wryan67/5x7laser/photos/8A266A81-EDB7-455D-8486-B8DF81140D3A-2090-000001E31C5A7B8D.jpg

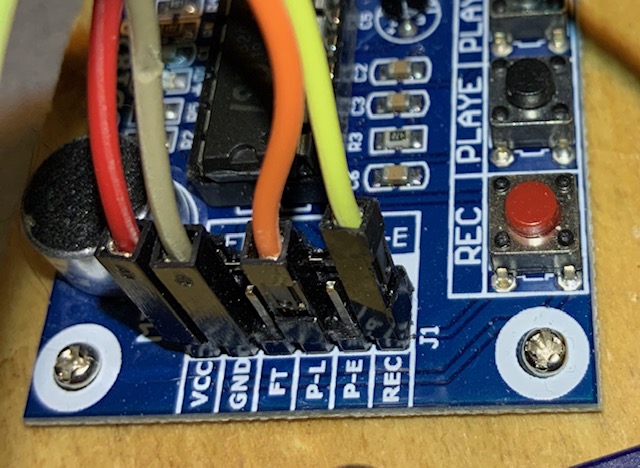
photos/8A266A81-EDB7-455D-8486-B8DF81140D3A-2090-000001E31C5A7B8D.jpg
