wryan67/5x7laser/photos/98A164D9-7E31-4DEC-9D0F-0AE598D2B0AE-2090-000001E5097991B9.jpg

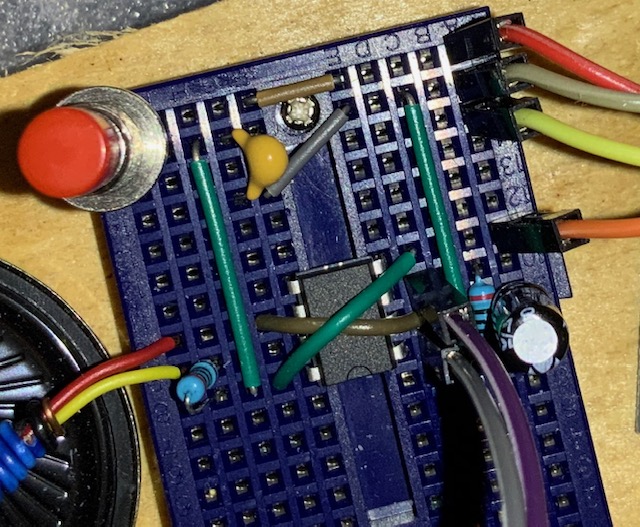
photos/98A164D9-7E31-4DEC-9D0F-0AE598D2B0AE-2090-000001E5097991B9.jpg
