wryan67/5x7laser/photos/C36D4584-9315-4CFA-A101-77AC29264F38-2090-000001E413C061C7.jpg

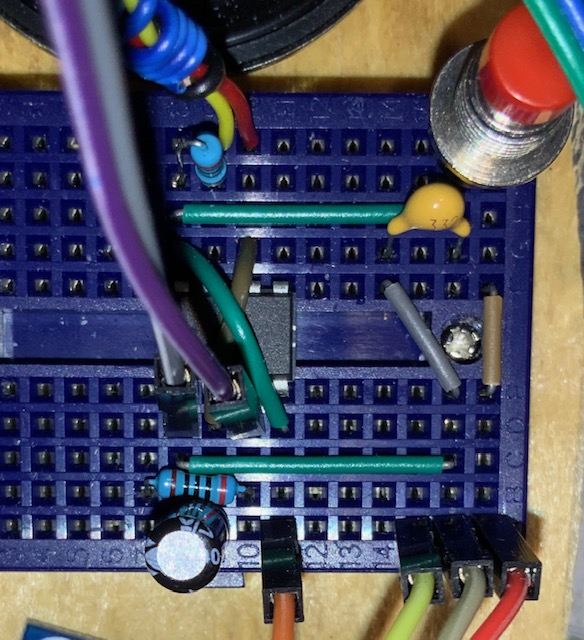
photos/C36D4584-9315-4CFA-A101-77AC29264F38-2090-000001E413C061C7.jpg
