wryan67/5x7laser/case/cnc/20mm spacer.dxf

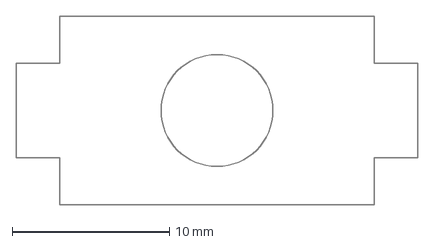
[picture p24: CAD file, 2023-05-02]
case/cnc/20mm spacer.dxf
25.5 x 12.0 mm
