wryan67/5x7laser/case/laser/save/plot-handle.dxf

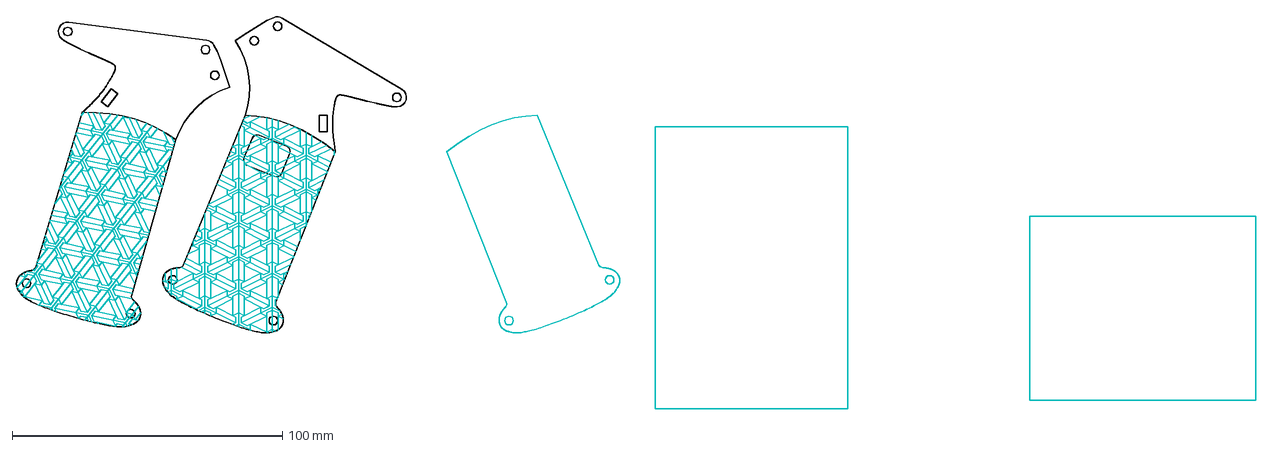
[picture p26: CAD file, 2023-05-02]
case/laser/save/plot-handle.dxf
458.9 x 145.3 mm
