wryan67/5x7laser/case/cnc/spacers.dxf

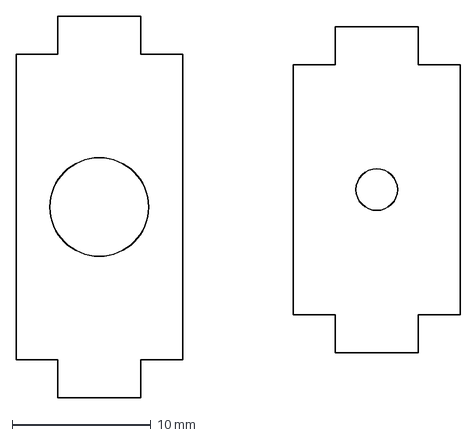
[picture p27: CAD file, 2023-05-02]
case/cnc/spacers.dxf
32.0 x 27.5 mm
