wryan67/5x7laser/case/laser/save/plot-case2m.dxf

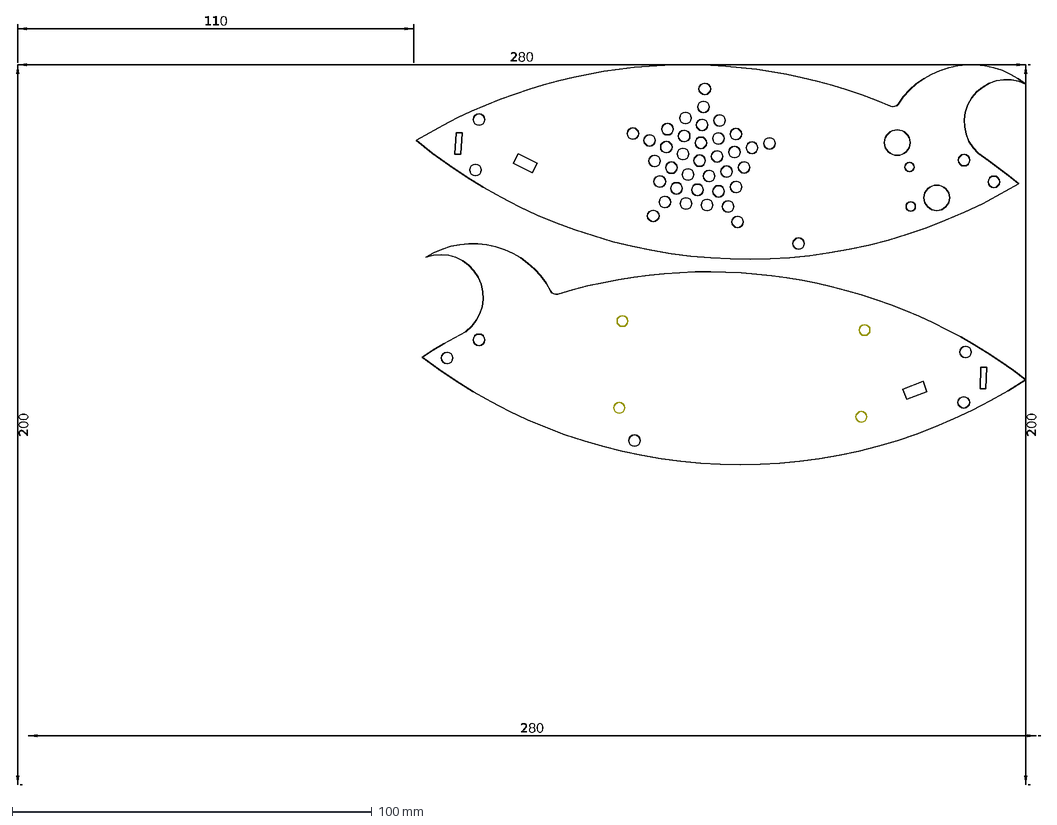
[picture p28: CAD file, 2023-05-02]
case/laser/save/plot-case2m.dxf
200
280
110
