wryan67/5x7laser/case/cnc/plot-handle-back.dxf

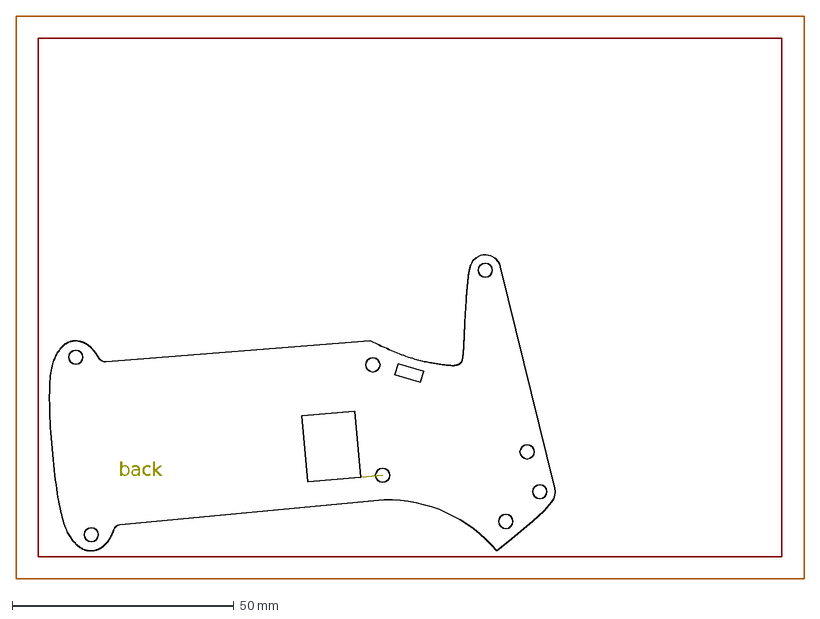
[picture p29: CAD file, 2023-05-02]
case/cnc/plot-handle-back.dxf
back
