wryan67/5x7laser/case/laser/plot-case2m.dxf

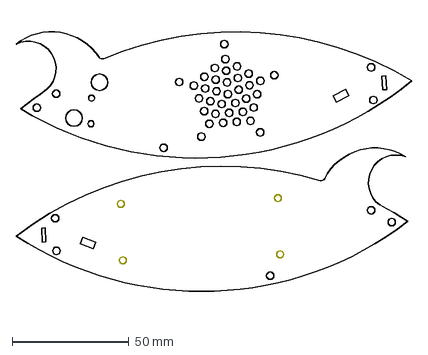
[picture p30: CAD file, 2023-05-02]
case/laser/plot-case2m.dxf
169.3 x 127.8 mm
