wryan67/5x7laser/case/laser/save/plot-case1f.dxf

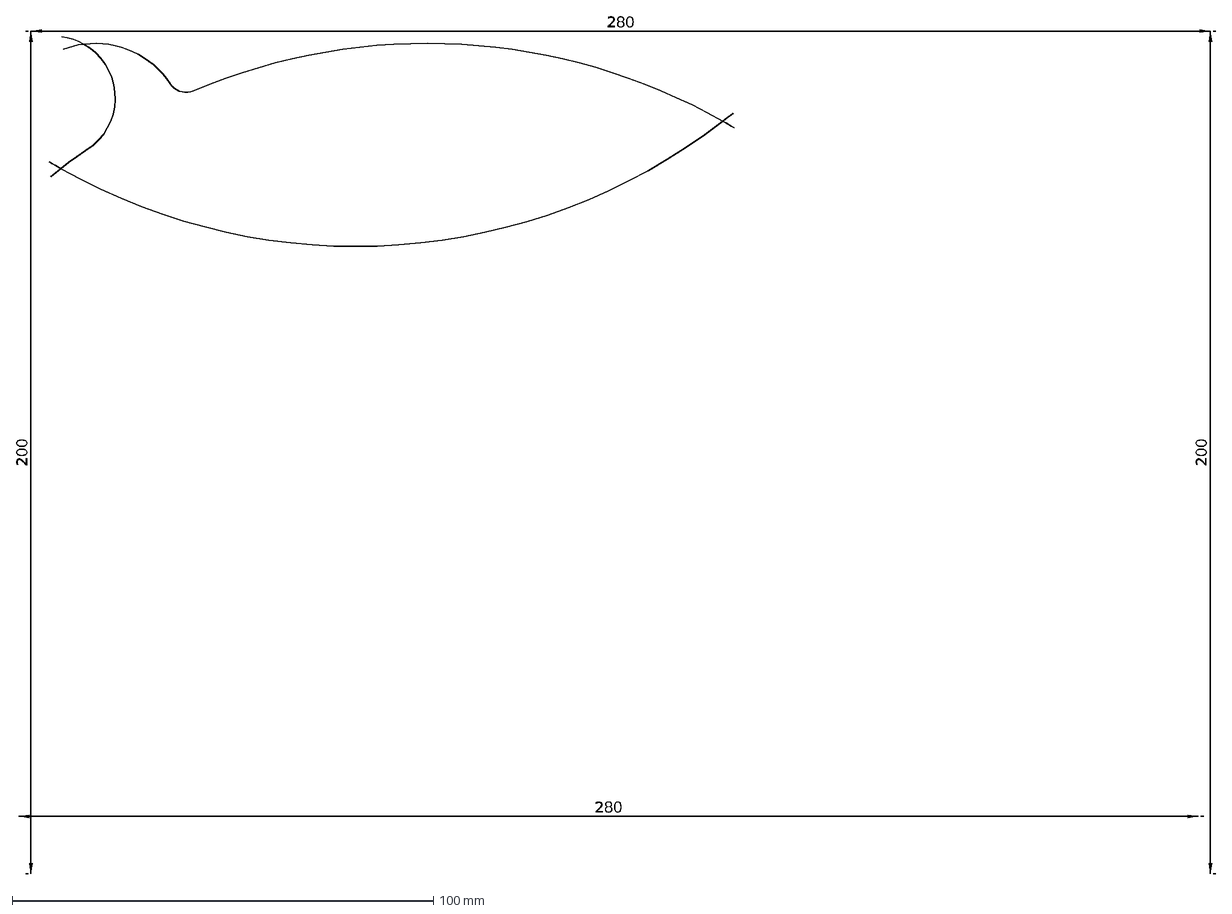
[picture p31: CAD file, 2023-05-02]
case/laser/save/plot-case1f.dxf
200
280
