wryan67/5x7laser/case/cnc/lasergun8.dxf

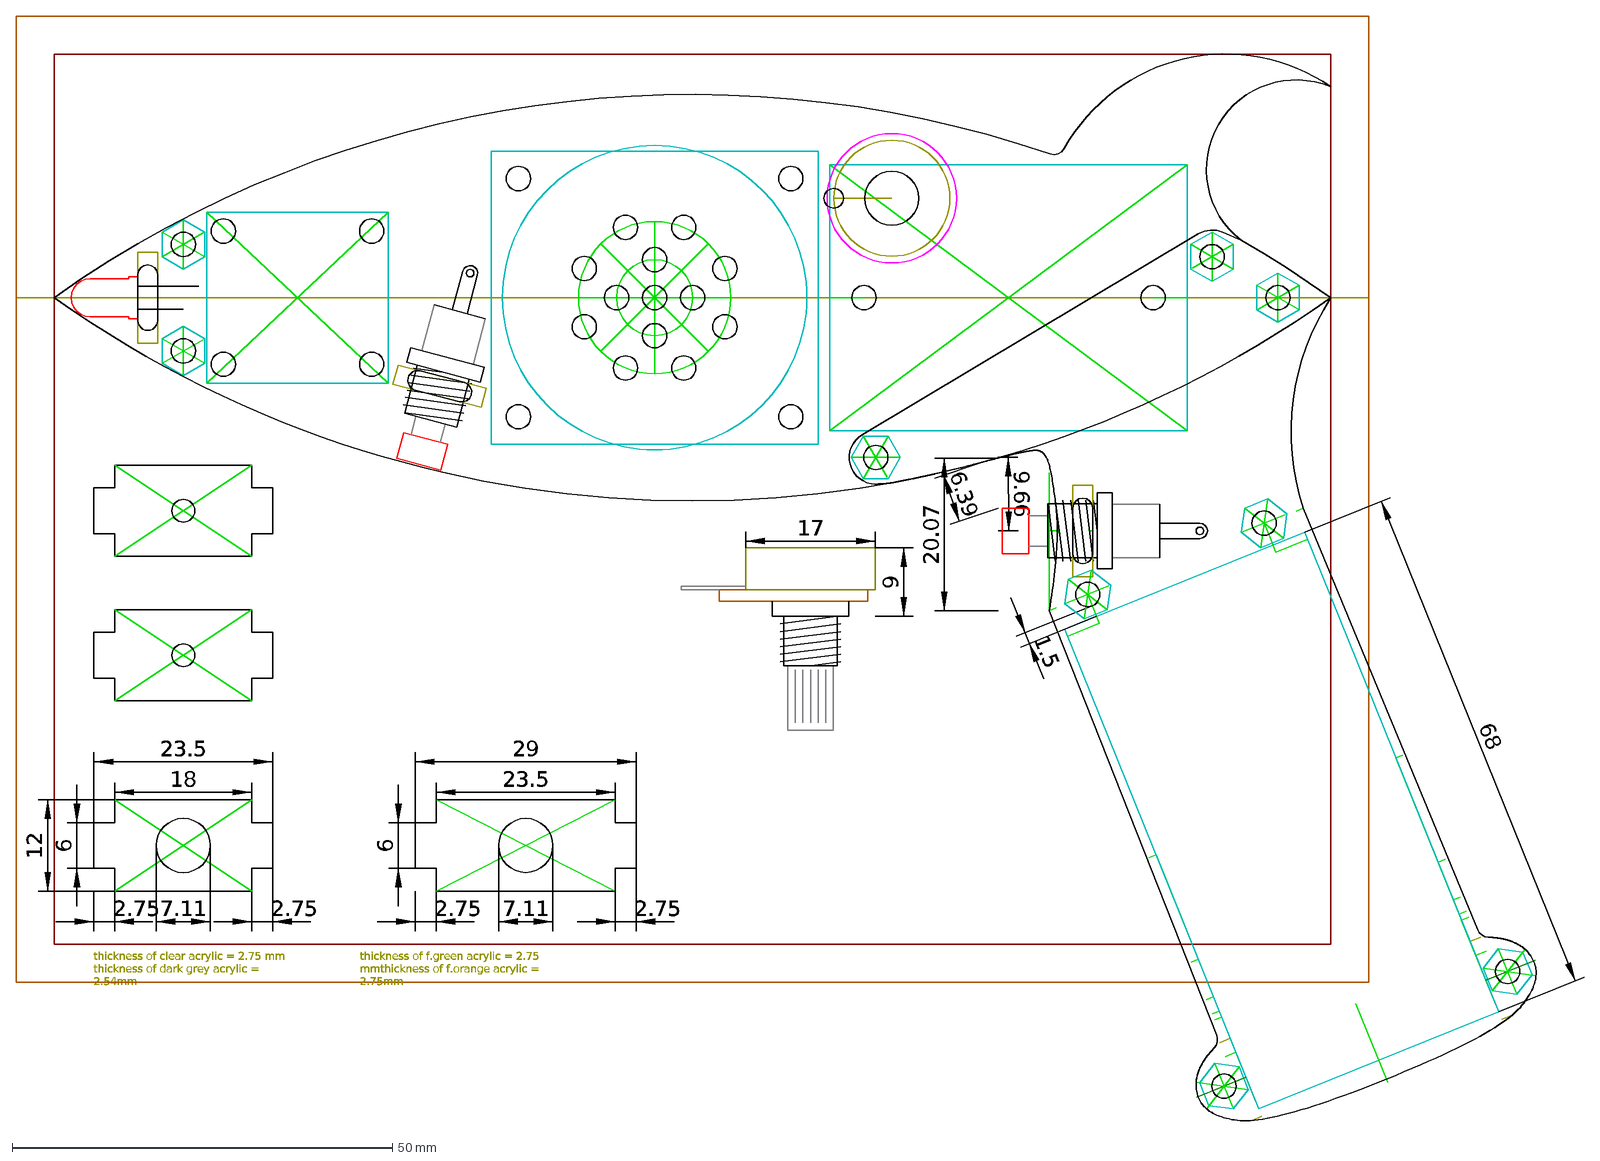
[picture p32: CAD file, 2023-05-02]
case/cnc/lasergun8.dxf
9
17
thickness of clear acrylic = 2.75 mm thickness of dark grey acrylic = 2.54mm
6
2.75
6.39
20.07
9.66
18
23.5
7.11
29
thickness of f.green acrylic = 2.75 mm thickness of f.orange acrylic = 2.75mm
1.5
68
12
