wryan67/5x7laser/case/laser/save/plot-case2f.dxf

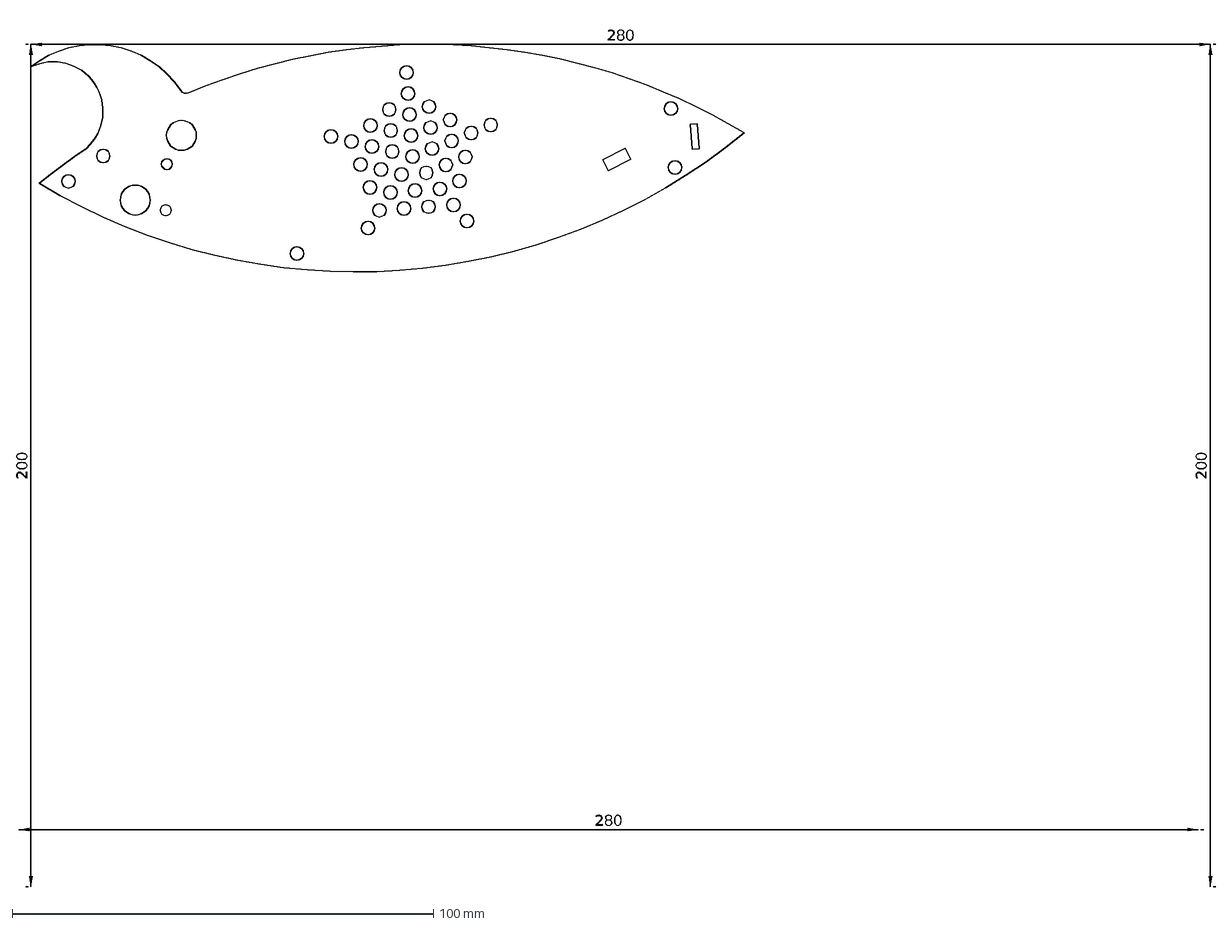
[picture p33: CAD file, 2023-05-02]
case/laser/save/plot-case2f.dxf
200
280
