wryan67/5x7laser/case/cnc/plot-spacers.dxf

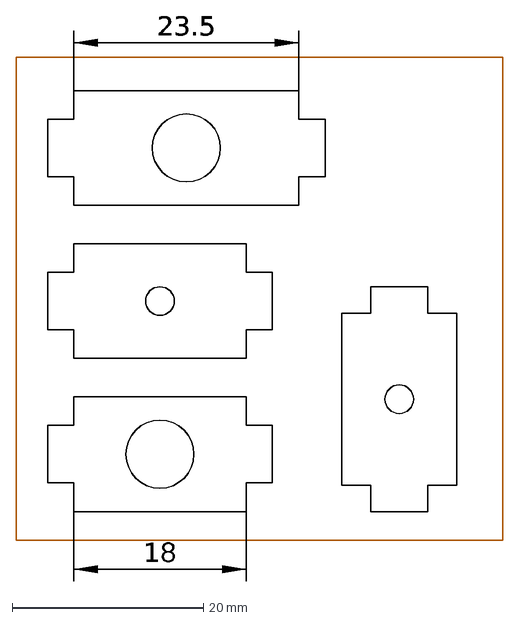
[picture p34: CAD file, 2023-05-02]
case/cnc/plot-spacers.dxf
23.5
18
