wryan67/5x7laser/case/laser/plot-spacers.dxf

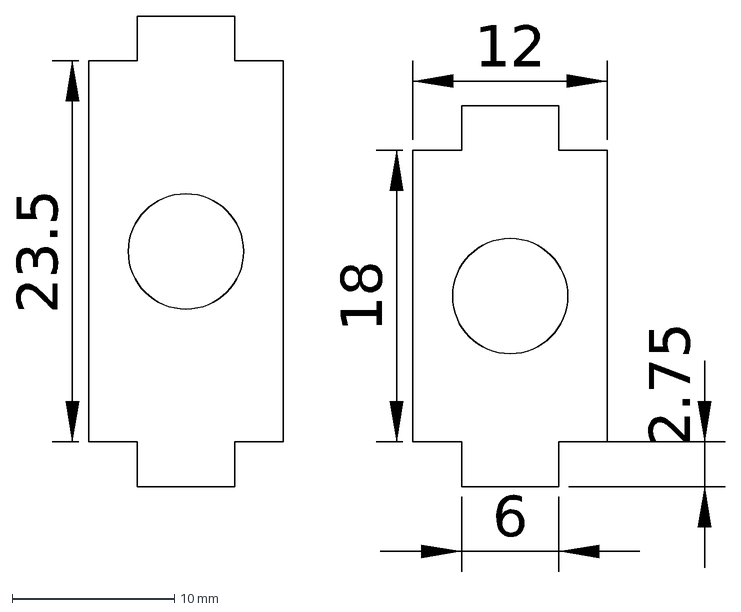
[picture p35: CAD file, 2023-05-02]
case/laser/plot-spacers.dxf
18
23.5
12
6
2.75
