wryan67/5x7laser/case/laser/save/plot-case2.dxf

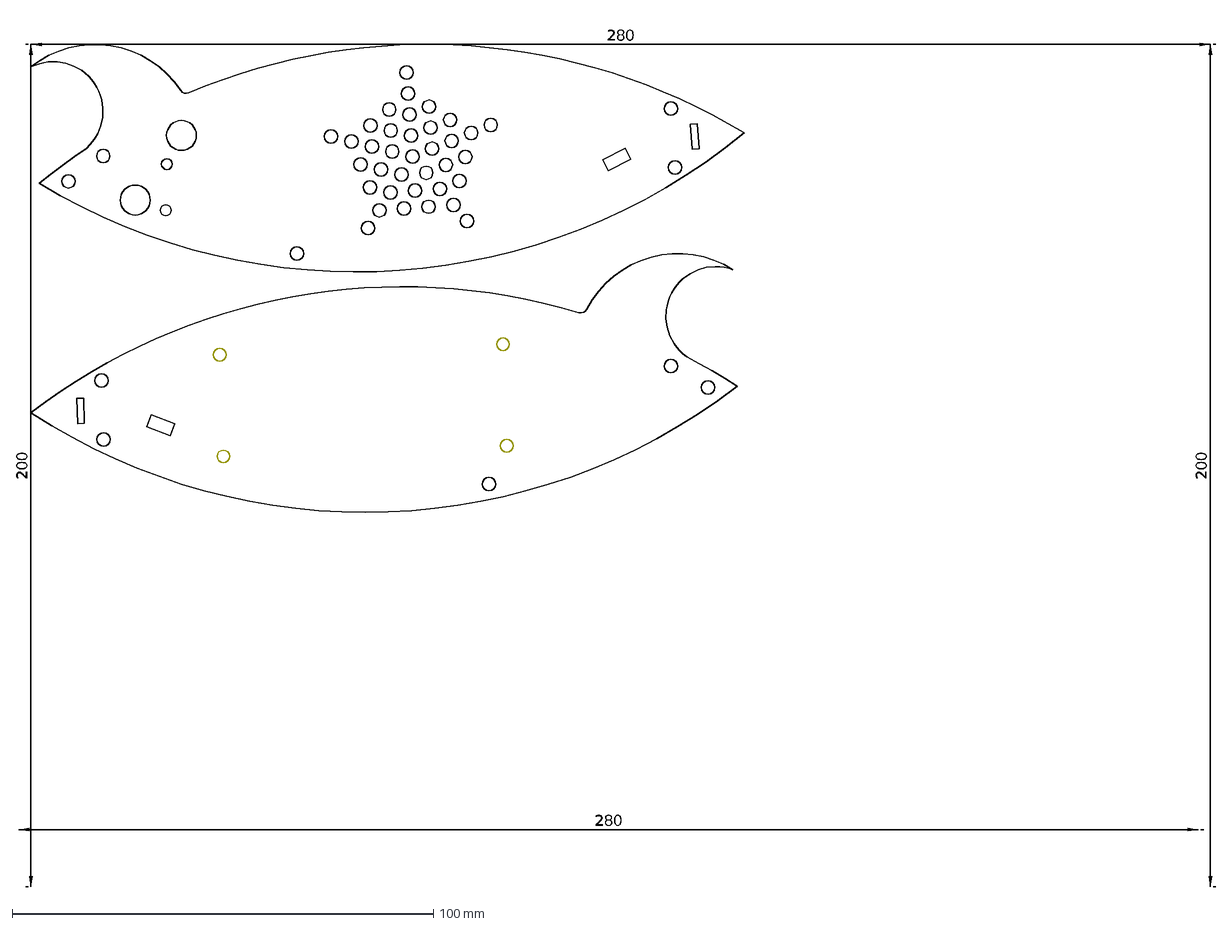
[picture p36: CAD file, 2023-05-02]
case/laser/save/plot-case2.dxf
200
280
