wryan67/5x7laser/case/cnc/plot-handle.dxf

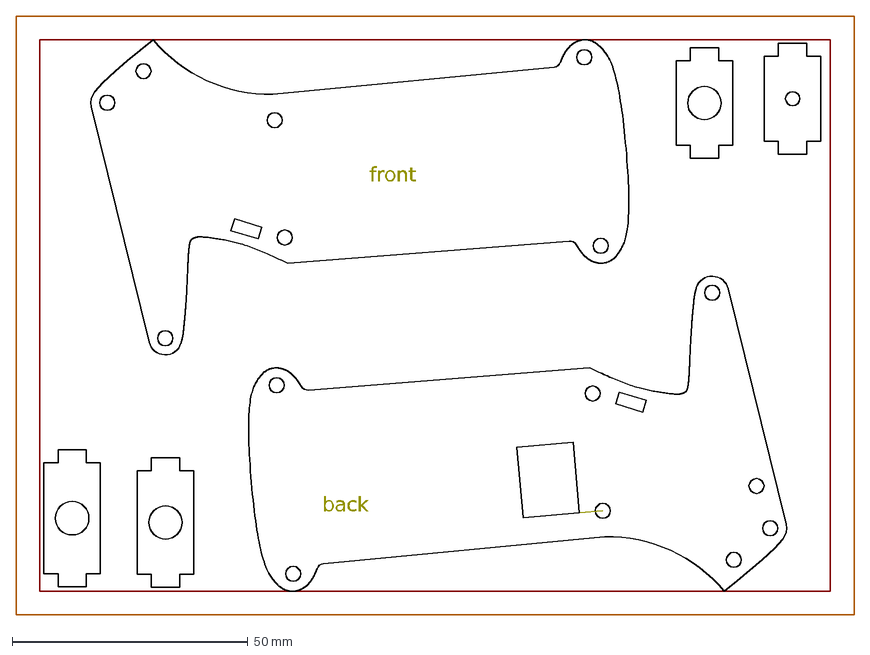
[picture p37: CAD file, 2023-05-02]
case/cnc/plot-handle.dxf
front
back
