wryan67/5x7laser/case/laser/save/plot-case1m.dxf

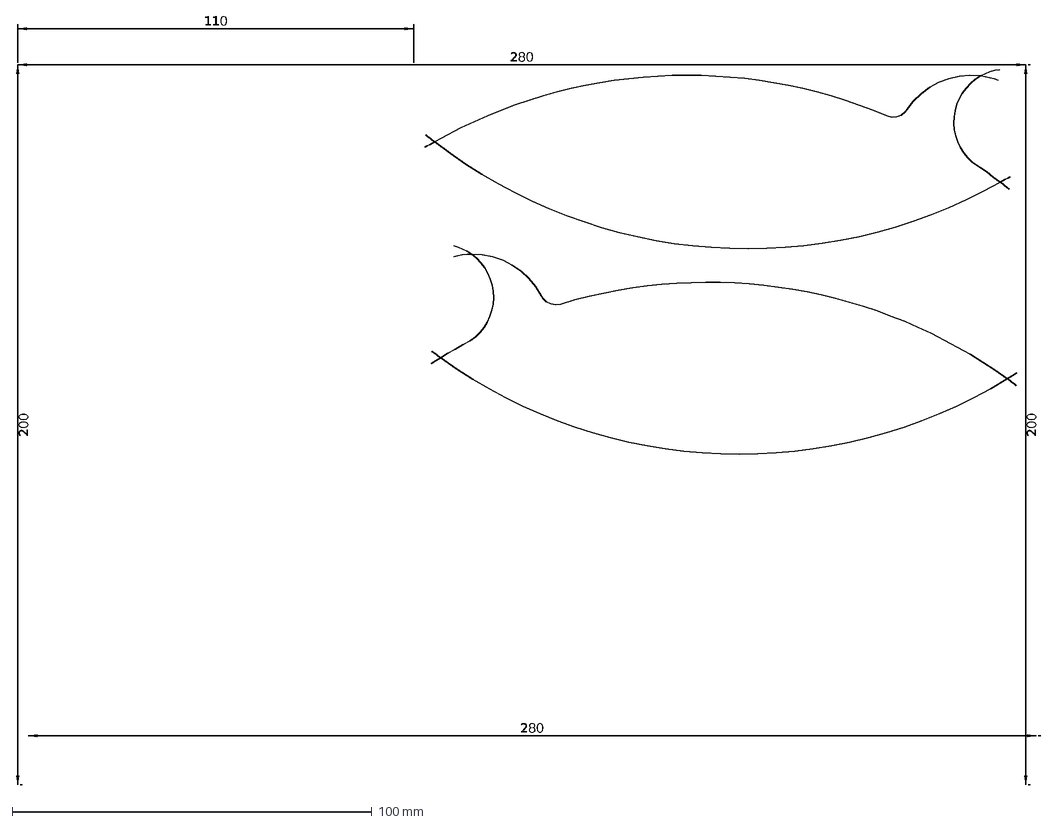
[picture p38: CAD file, 2023-05-02]
case/laser/save/plot-case1m.dxf
200
280
110
