wryan67/5x7laser/case/laser/spacers.dxf

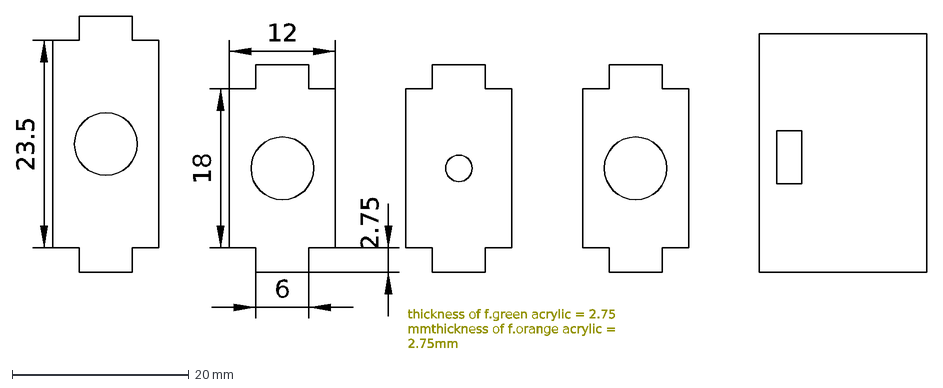
[picture p39: CAD file, 2023-05-02]
case/laser/spacers.dxf
18
23.5
12
6
2.75
thickness of f.green acrylic = 2.75 mm thickness of f.orange acrylic = 2.75mm
