wryan67/5x7laser/case/laser/plot-case1.dxf

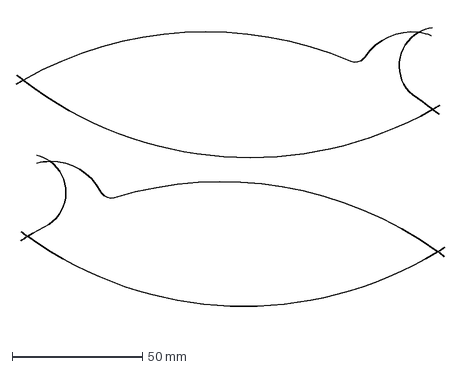
[picture p40: CAD file, 2023-05-02]
case/laser/plot-case1.dxf
164.5 x 120.3 mm
