wryan67/5x7laser/case/laser/save/plot2.dxf

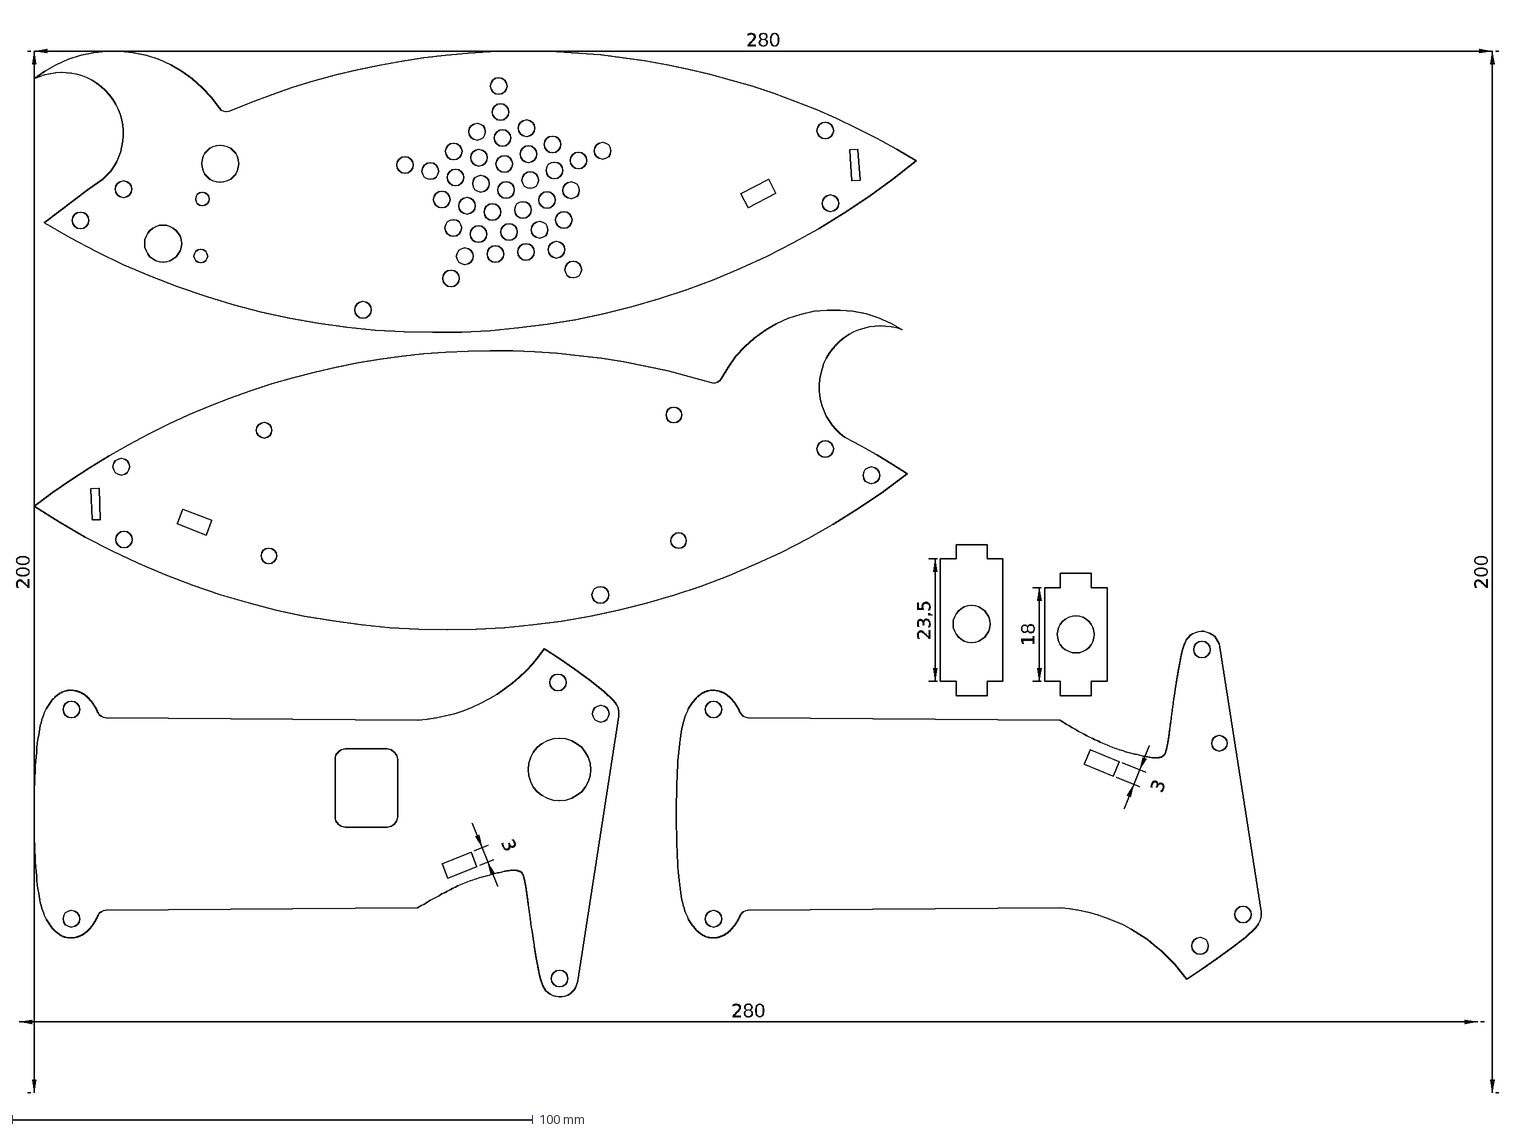
[picture p41: CAD file, 2023-05-02]
case/laser/save/plot2.dxf
200
280
3
18
23,5
