wryan67/5x7laser/case/laser/save/controller-pcb.dxf

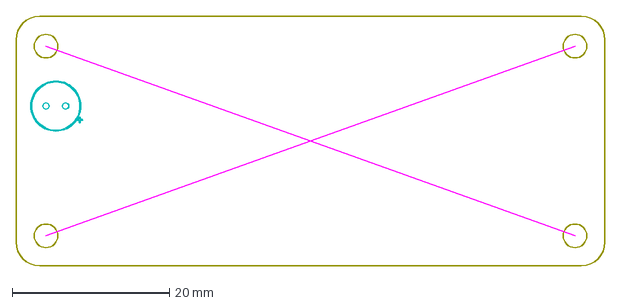
[picture p43: CAD file, 2023-05-02]
case/laser/save/controller-pcb.dxf
74.9 x 31.8 mm
