wryan67/5x7laser/case/laser/plot-handle1m.dxf

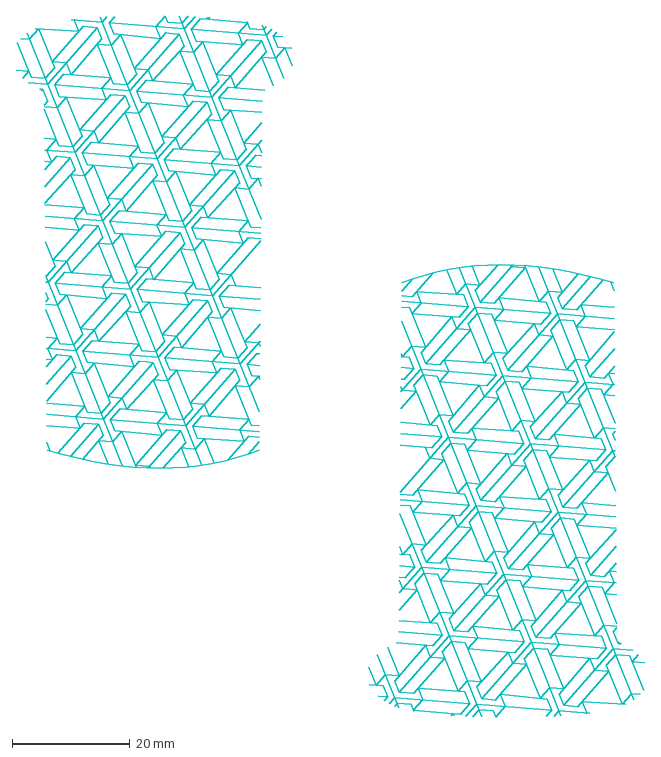
[picture p44: CAD file, 2023-05-02]
case/laser/plot-handle1m.dxf
106.6 x 118.9 mm
