wryan67/5x7laser/case/laser/plot-handle2m.dxf

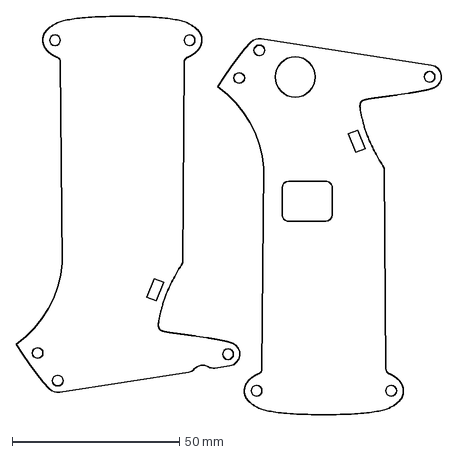
[picture p45: CAD file, 2023-05-02]
case/laser/plot-handle2m.dxf
127.2 x 119.0 mm
