wryan67/5x7laser/case/laser/plot-case2.dxf

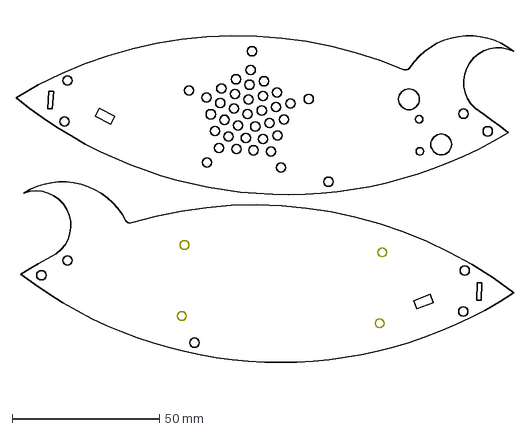
[picture p46: CAD file, 2023-05-02]
case/laser/plot-case2.dxf
169.3 x 127.8 mm
