wryan67/5x7laser/case/laser/plot-handle2.dxf

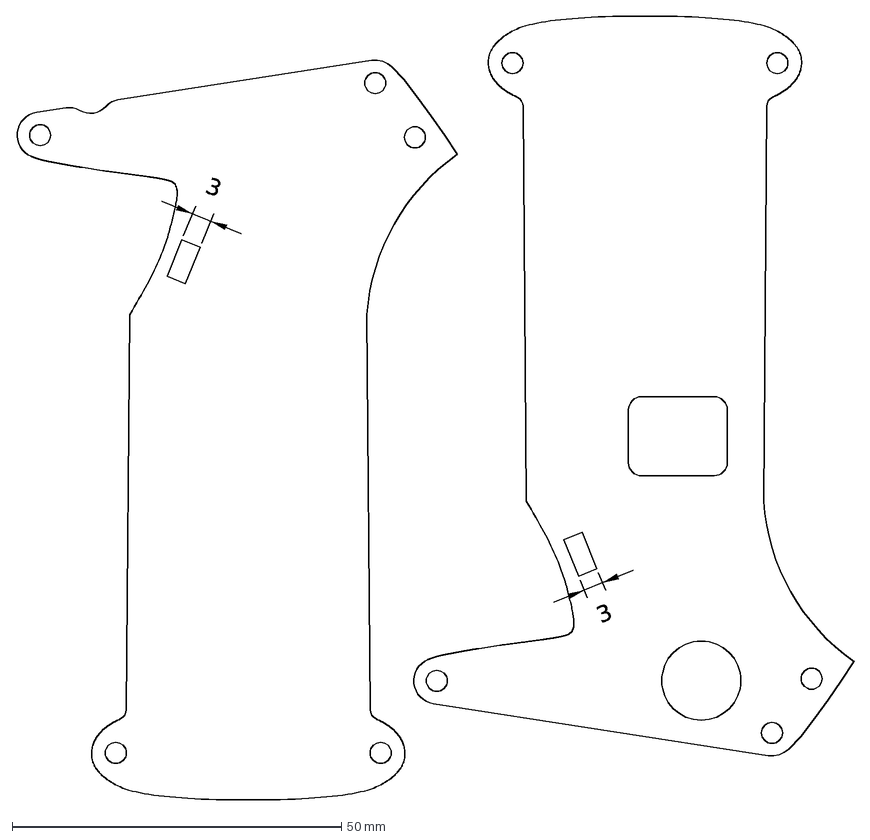
[picture p47: CAD file, 2023-05-02]
case/laser/plot-handle2.dxf
3
